Bei-er/wiggle-spine/doc/ltspice-simulations/dmx512-isolator.asc

A1: and; Vhigh=5
A2: and; Vhigh=5
A3: inv; Vhigh=5
C1: cap; 12µ; Rser=7.1m Lser=0 mfg="KEMET" pn="C1206C126K8PAC" type="X5R"
C2: cap; 1n; Rser=689.1m Lser=0 mfg="   ---" pn="   ---" type="   ---"
C3: cap; .1µ
C4: cap; .1µ
C5: cap; .1µ
C7: cap; 1n
D1: schottky; BAT54
D2: schottky; BAT54
D3: schottky; BAT54
L1: ind2; 175µ; Rser=.1
L2: ind2; 175µ; Rser=.1
L3: ind2; 175µ; Rser=.1
L4: ind2; 175µ; Rser=.1
L5: ind2; 175µ; Rser=.1
L6: ind2; 175µ; Rser=.1
L7: ind2; 175µ; Rser=.1
L8: ind2; 175µ; Rser=.1
M1: nmos; IRFML8244
M2: nmos; IRFML8244
R1: res; 150
R2: res; 4.7k
R3: res; 4.7k
R4: res; 100
R7: res; 1meg
U1: 74hct14
U2: LTC2862-1
U3: 74hct14
U4: 74hct14
U5: 74hct14
U6: 74hct14
V1: voltage; 5; Rser=1m
V2: voltage; PULSE(5 0 1u 0 0 .8u 6u)
V4: voltage; PULSE(5 0 4u 0 0 .8u 6u)
V5: voltage; PULSE(0 5 1u 0 0 9u 10u)
V6: voltage; PULSE(0 5 0 0 0 25n 50n)
Named nets: 0, D+, D-
K0 L1 L2 L3 L4 1
.tran 0 10m 1n
.include 74hct.lib
K1 L5 L6 L7 L8 1
NC7WZ14P6X
